CedarGroveStudios/Musique_Concrete_Clock/PCB/Musique_Concrete_Clock.png

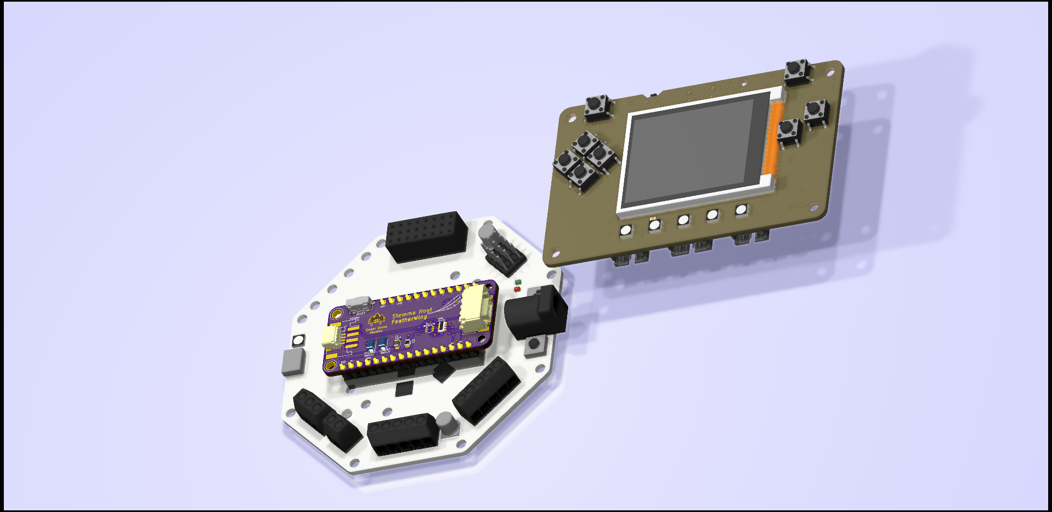
PCB/Musique_Concrete_Clock.png
