CedarGroveStudios/Musique_Concrete_Clock/photos and graphics/DSC06083 2.jpeg

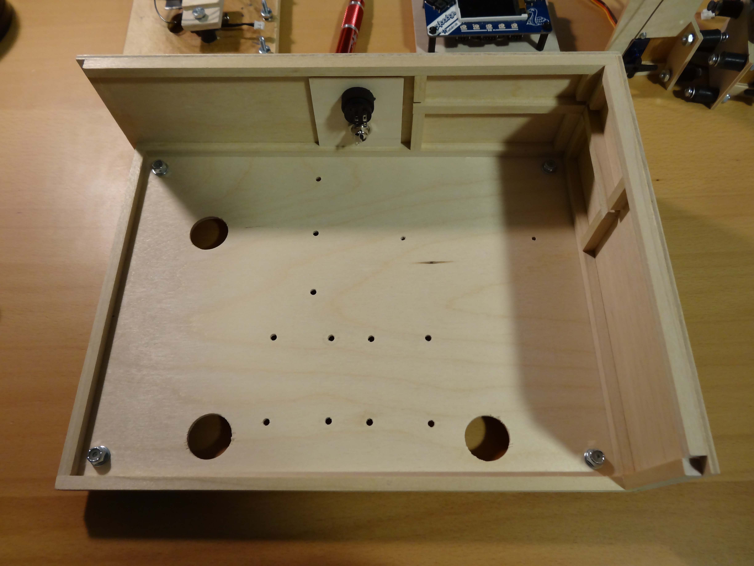
photos and graphics/DSC06083 2.jpeg
