CedarGroveStudios/Musique_Concrete_Clock/photos and graphics/DSC06085 2.jpeg

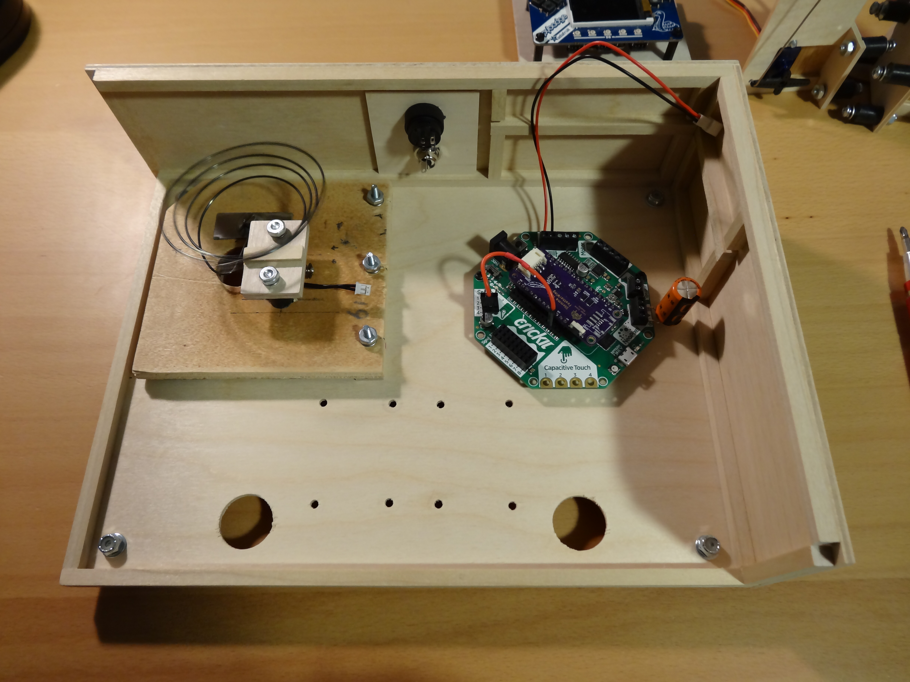
photos and graphics/DSC06085 2.jpeg
