CedarGroveStudios/Musique_Concrete_Clock/photos and graphics/DSC06090 2.jpeg

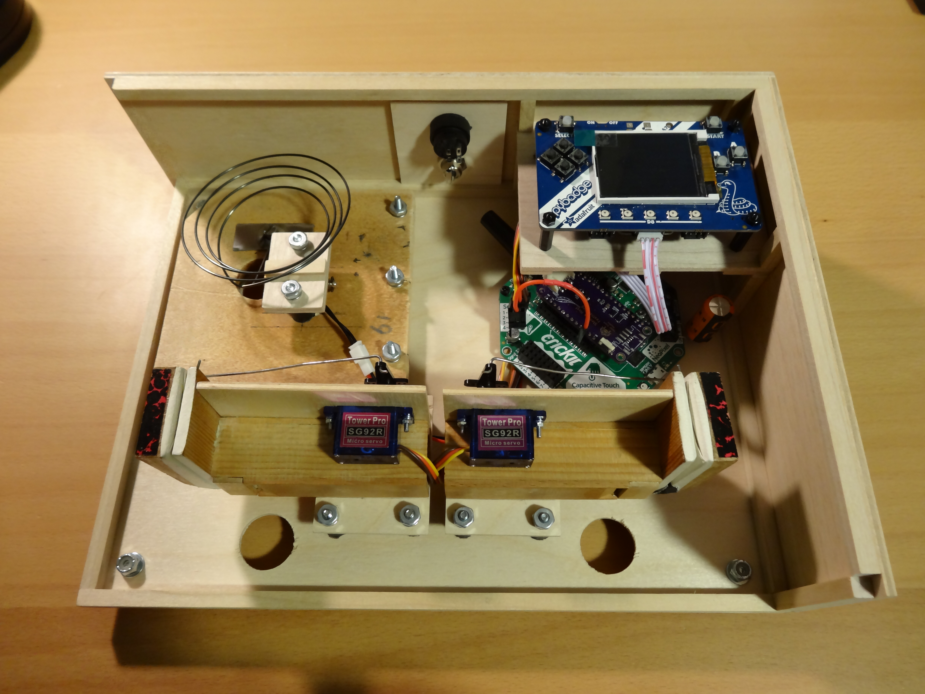
photos and graphics/DSC06090 2.jpeg
