CedarGroveStudios/Musique_Concrete_Clock/photos and graphics/DSC06091 2.jpeg

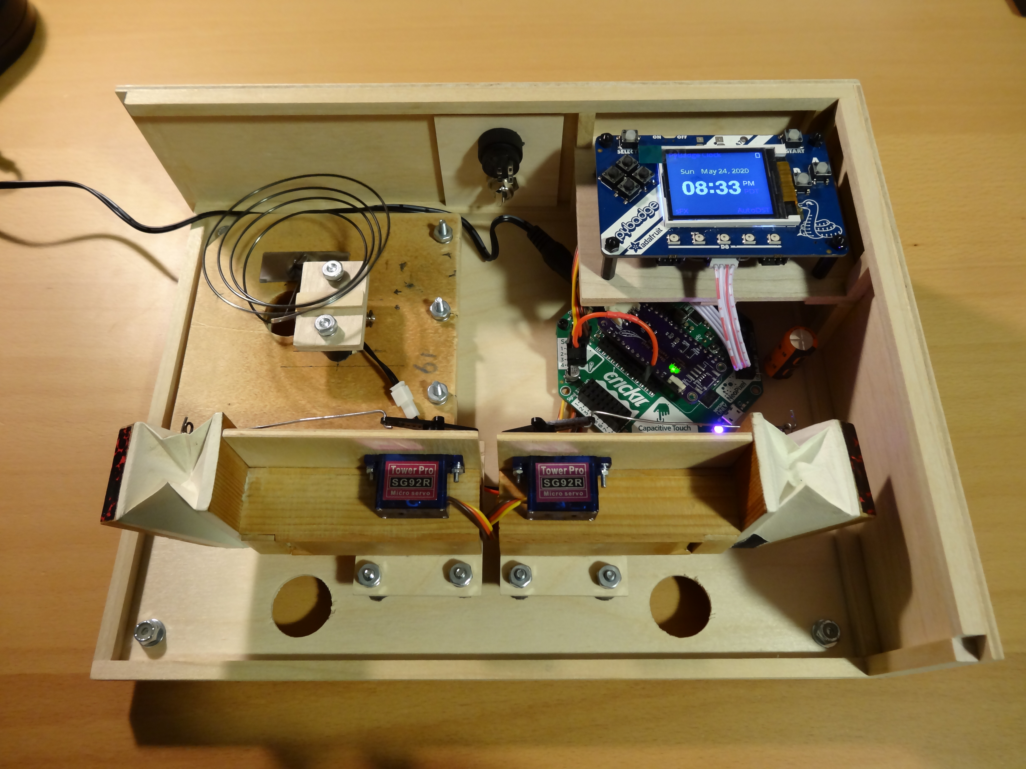
photos and graphics/DSC06091 2.jpeg
