CedarGroveStudios/Musique_Concrete_Clock/photos and graphics/DSC06096.jpeg

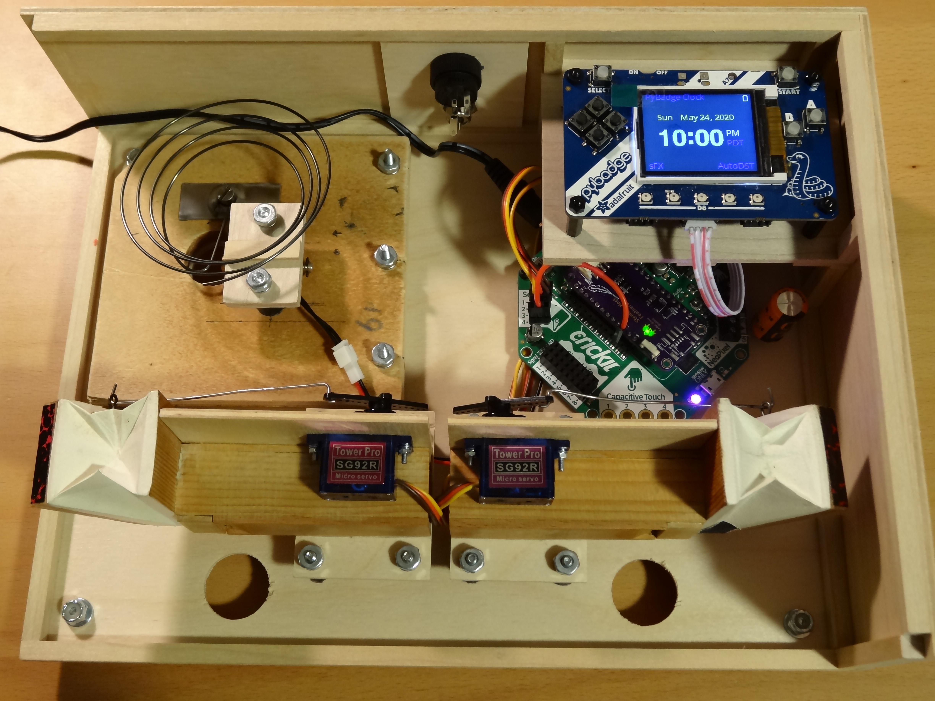
photos and graphics/DSC06096.jpeg
