CedarGroveStudios/Musique_Concrete_Clock/photos and graphics/IMG_0173.jpeg

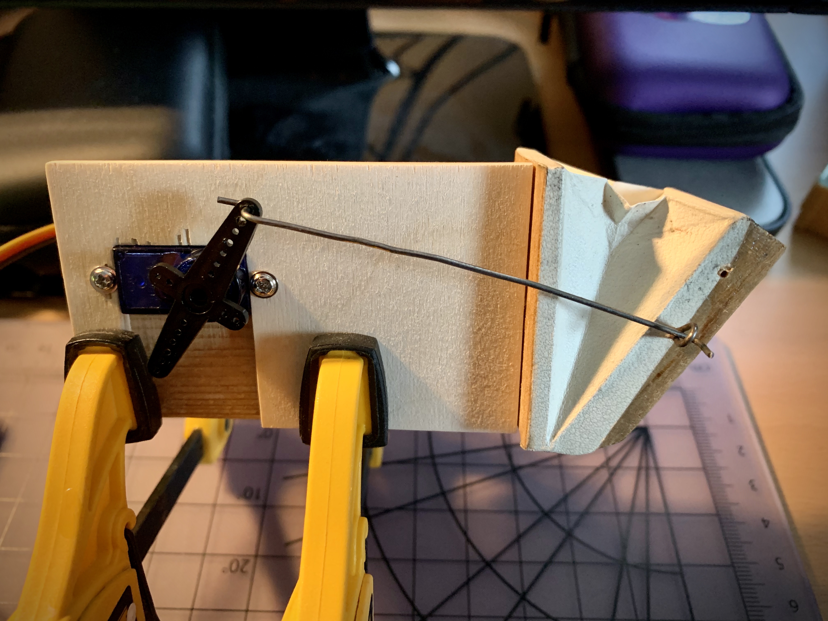
photos and graphics/IMG_0173.jpeg
