CedarGroveStudios/Musique_Concrete_Clock/photos and graphics/IMG_0174.jpeg

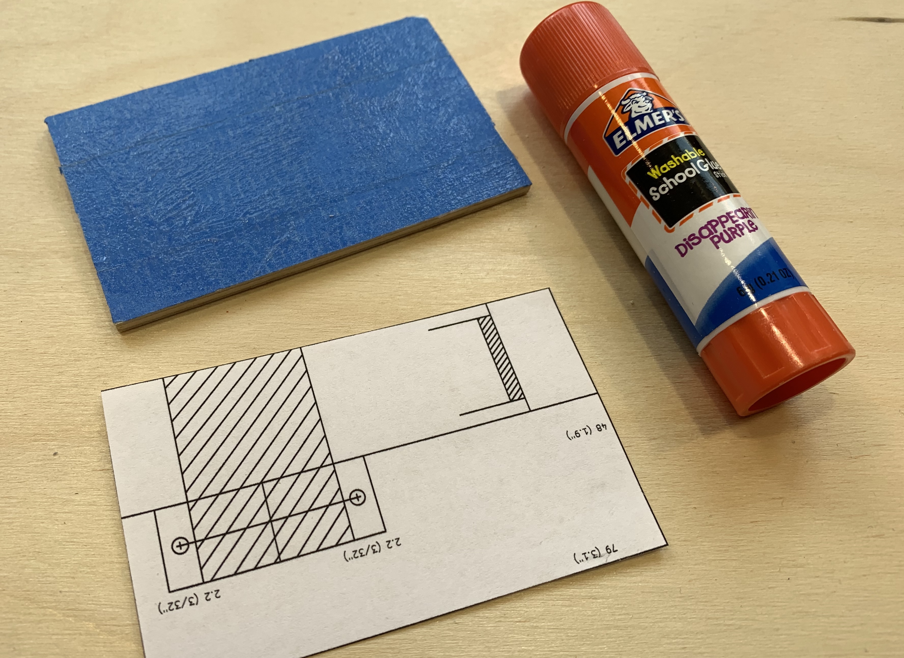
photos and graphics/IMG_0174.jpeg
