CedarGroveStudios/Musique_Concrete_Clock/photos and graphics/IMG_0175.jpeg

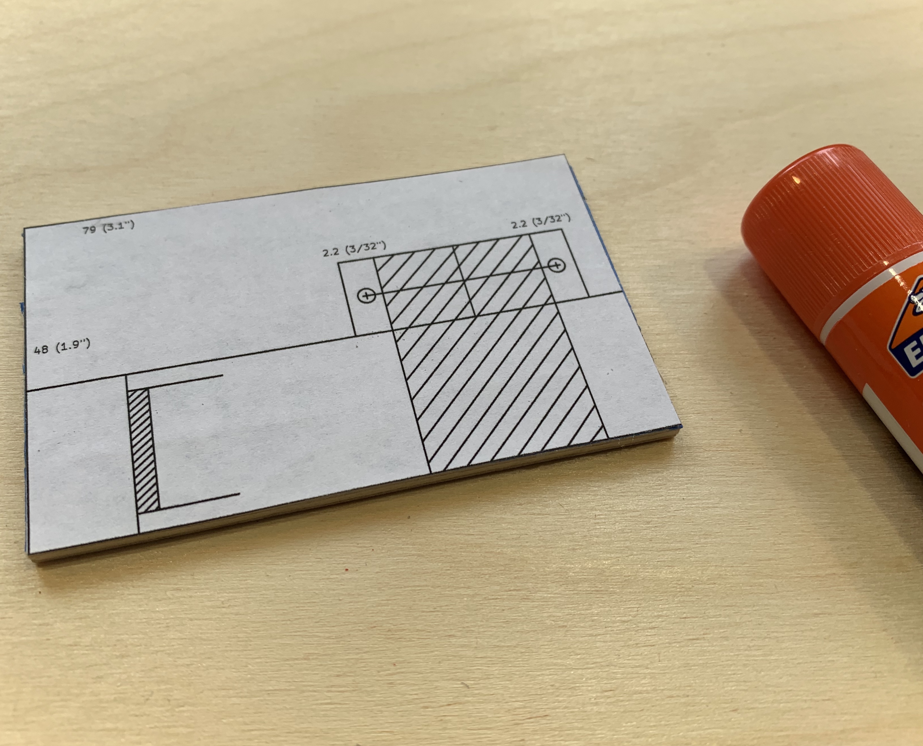
photos and graphics/IMG_0175.jpeg
