CedarGroveStudios/Musique_Concrete_Clock/photos and graphics/IMG_0176.jpeg

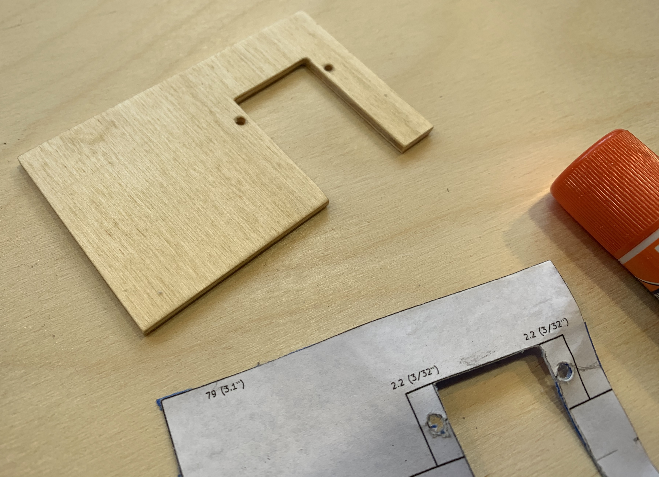
photos and graphics/IMG_0176.jpeg
