CedarGroveStudios/Musique_Concrete_Clock/photos and graphics/IMG_0180.jpg

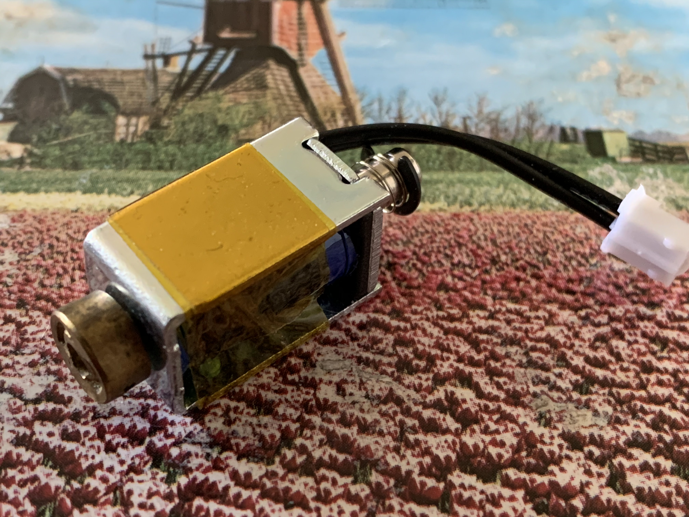
photos and graphics/IMG_0180.jpg
