CedarGroveStudios/Musique_Concrete_Clock/photos and graphics/IMG_0204.jpeg

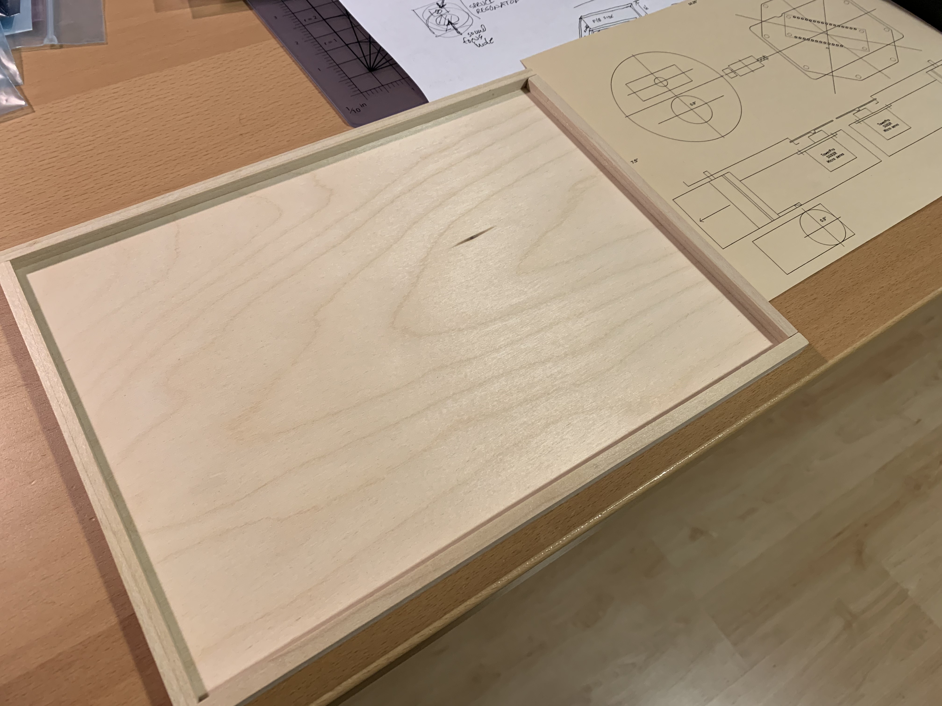
photos and graphics/IMG_0204.jpeg
