CedarGroveStudios/Musique_Concrete_Clock/photos and graphics/IMG_0205.jpeg

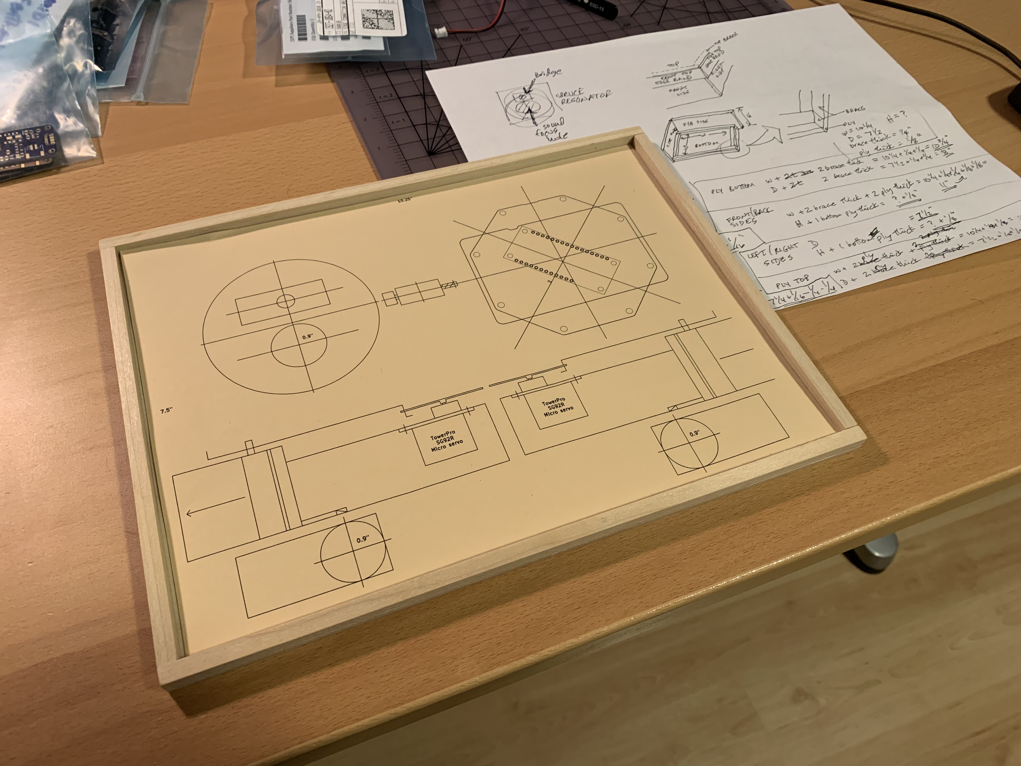
photos and graphics/IMG_0205.jpeg
