CedarGroveStudios/Musique_Concrete_Clock/photos and graphics/IMG_0206.jpeg

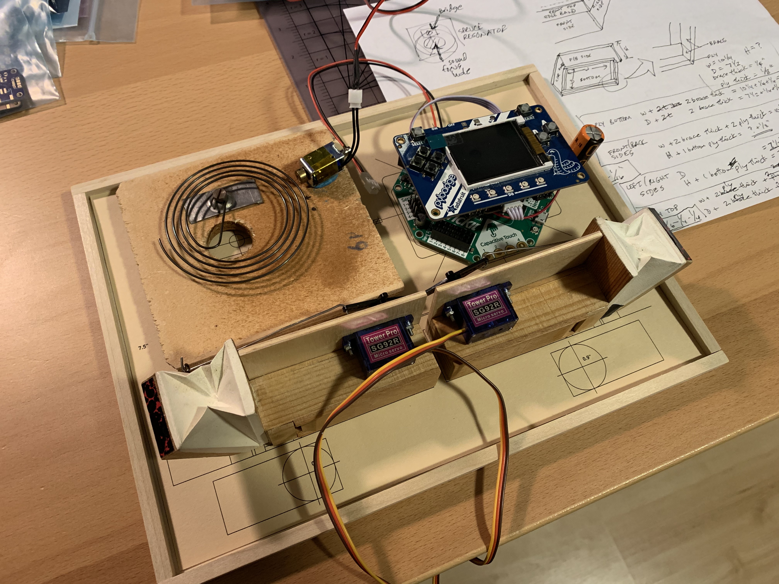
photos and graphics/IMG_0206.jpeg
