CedarGroveStudios/Musique_Concrete_Clock/photos and graphics/IMG_0208.jpeg

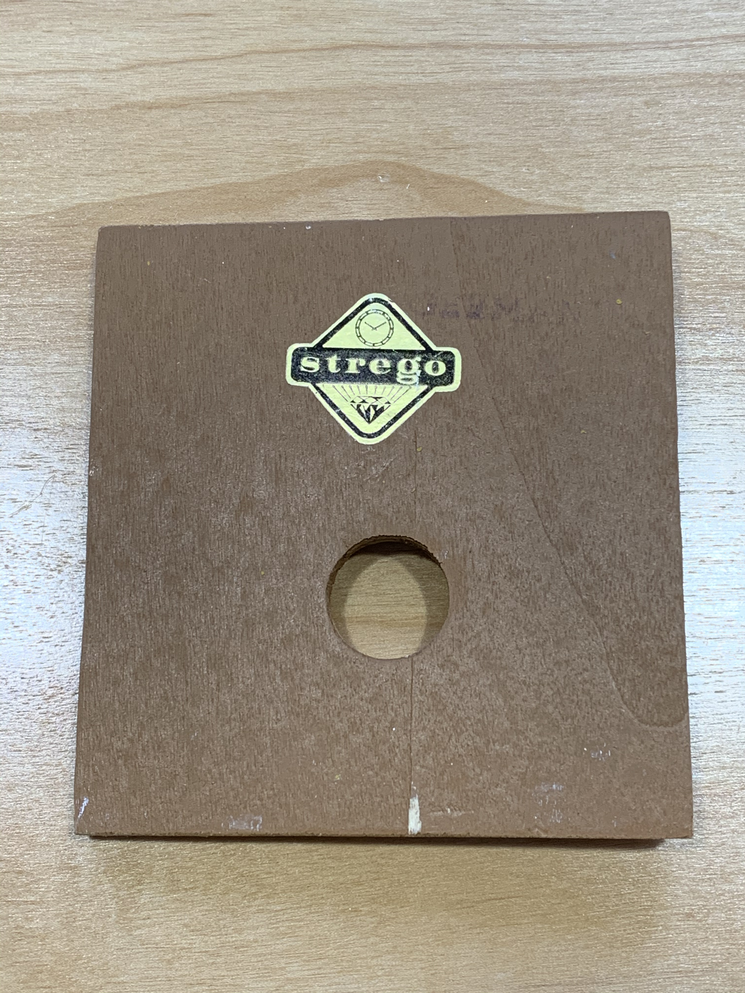
photos and graphics/IMG_0208.jpeg
