CedarGroveStudios/Musique_Concrete_Clock/photos and graphics/IMG_0209.jpeg

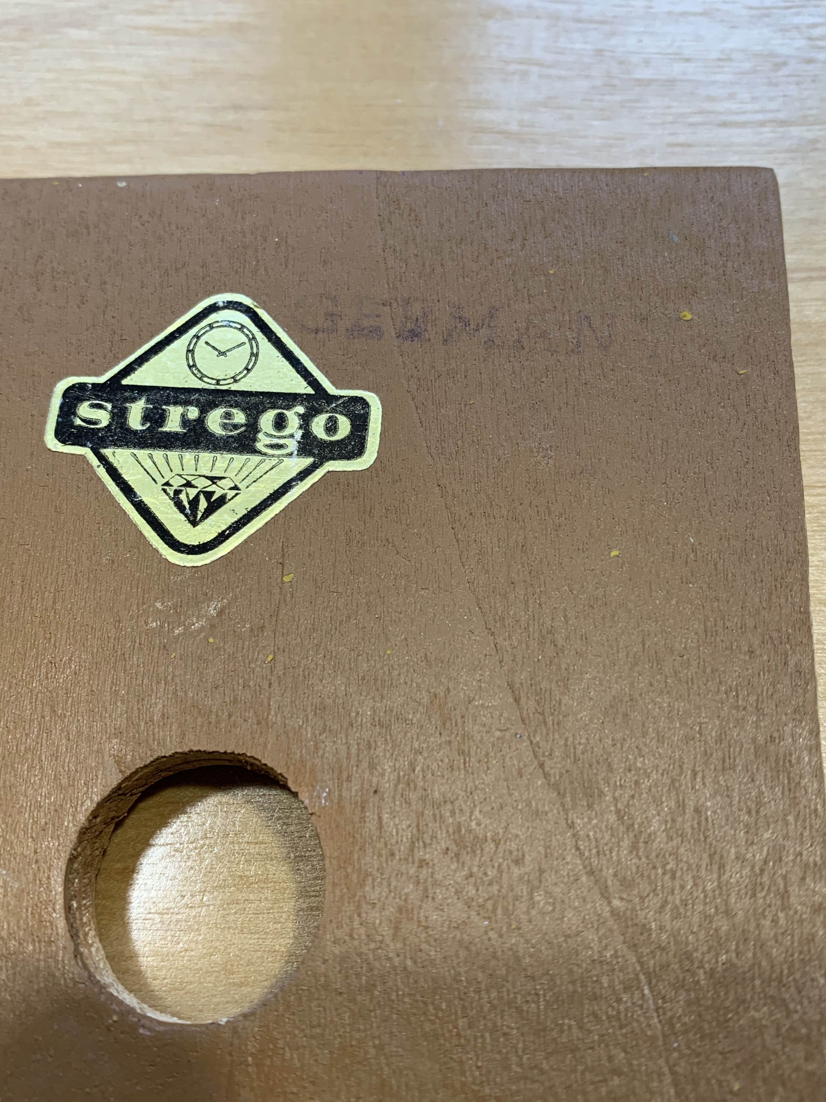
photos and graphics/IMG_0209.jpeg
