CedarGroveStudios/Musique_Concrete_Clock/photos and graphics/IMG_0211.jpeg

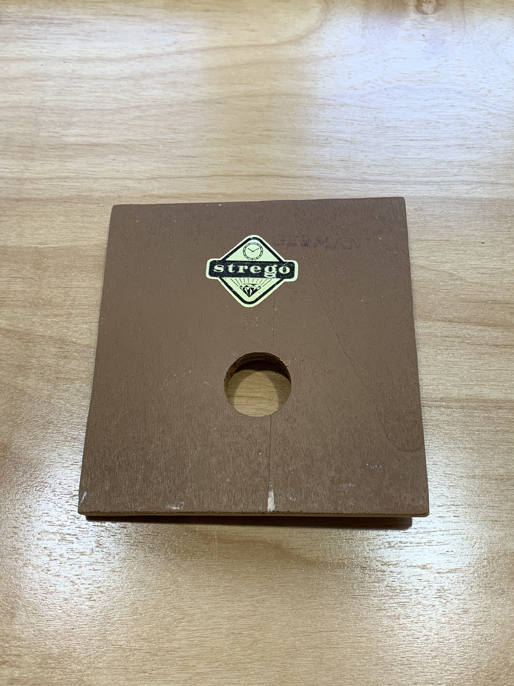
photos and graphics/IMG_0211.jpeg
