CedarGroveStudios/Musique_Concrete_Clock/photos and graphics/IMG_0227.jpeg

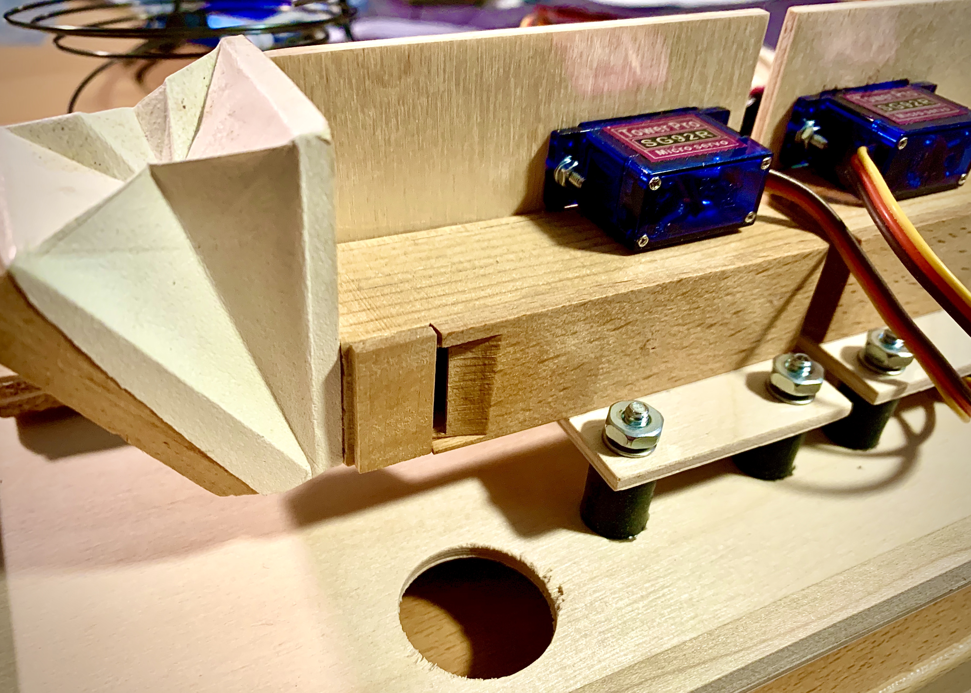
photos and graphics/IMG_0227.jpeg
