CedarGroveStudios/Musique_Concrete_Clock/photos and graphics/IMG_0228.jpeg

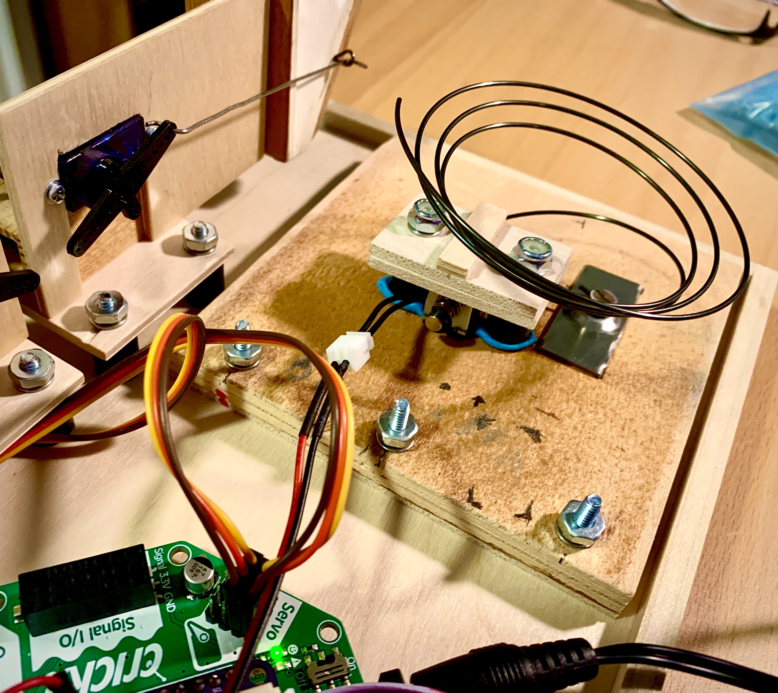
photos and graphics/IMG_0228.jpeg
