CedarGroveStudios/Musique_Concrete_Clock/photos and graphics/IMG_0229.jpeg

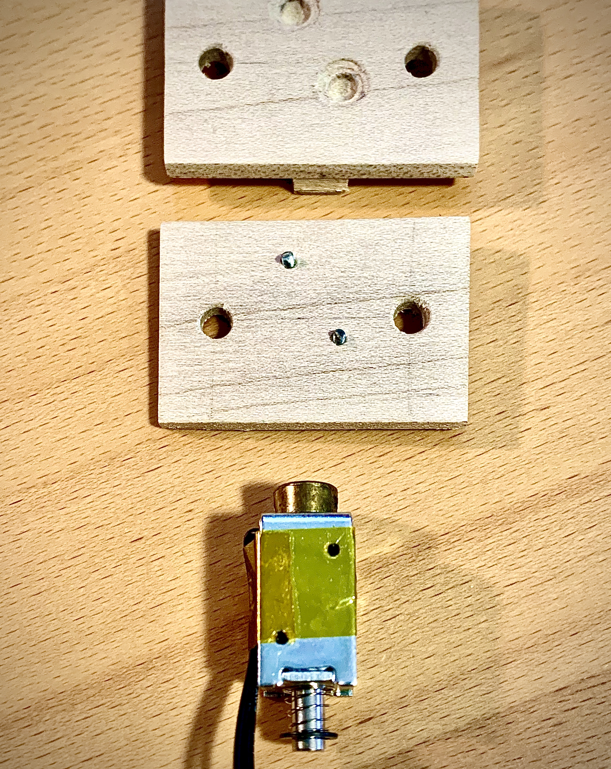
photos and graphics/IMG_0229.jpeg
