CedarGroveStudios/Musique_Concrete_Clock/photos and graphics/IMG_0232.jpeg

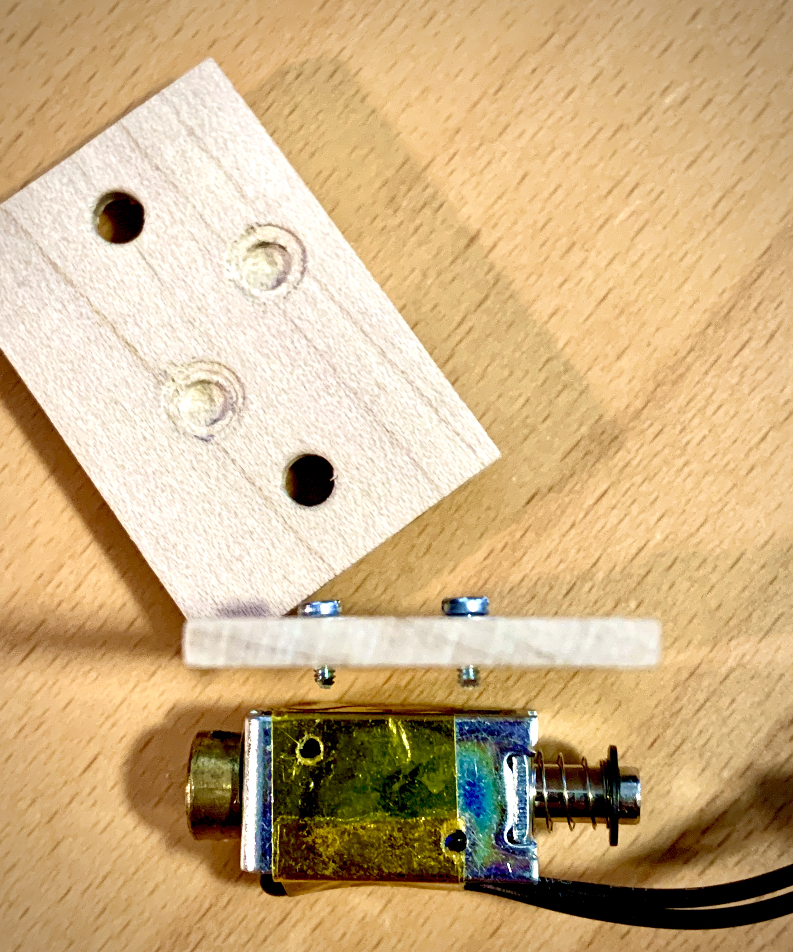
photos and graphics/IMG_0232.jpeg
