CedarGroveStudios/Musique_Concrete_Clock/photos and graphics/IMG_0235 2.jpeg

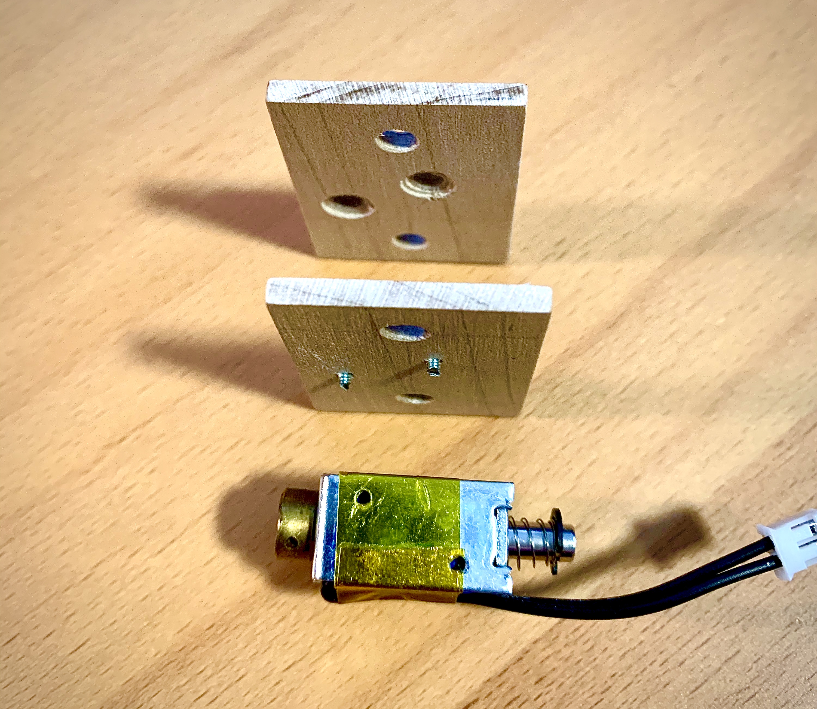
photos and graphics/IMG_0235 2.jpeg
