CedarGroveStudios/Musique_Concrete_Clock/photos and graphics/IMG_0237.jpeg

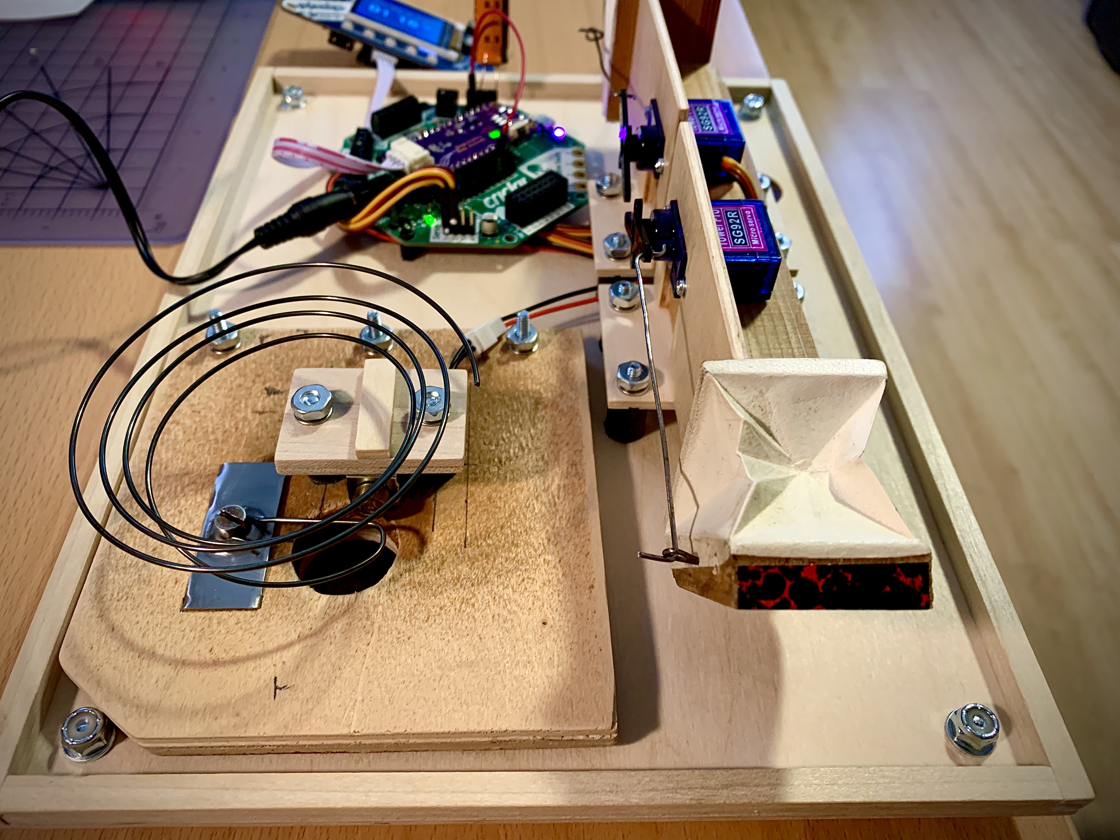
photos and graphics/IMG_0237.jpeg
