CedarGroveStudios/Musique_Concrete_Clock/photos and graphics/IMG_0238.jpeg

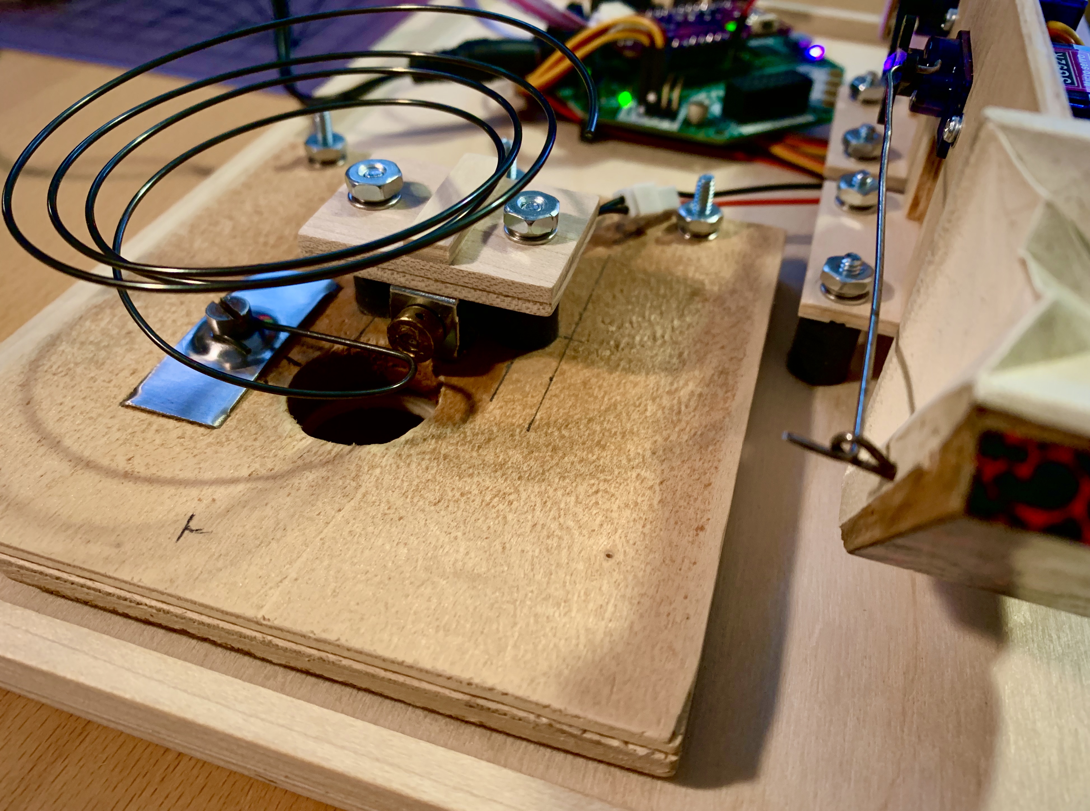
photos and graphics/IMG_0238.jpeg
