CedarGroveStudios/Musique_Concrete_Clock/photos and graphics/IMG_0239.jpeg

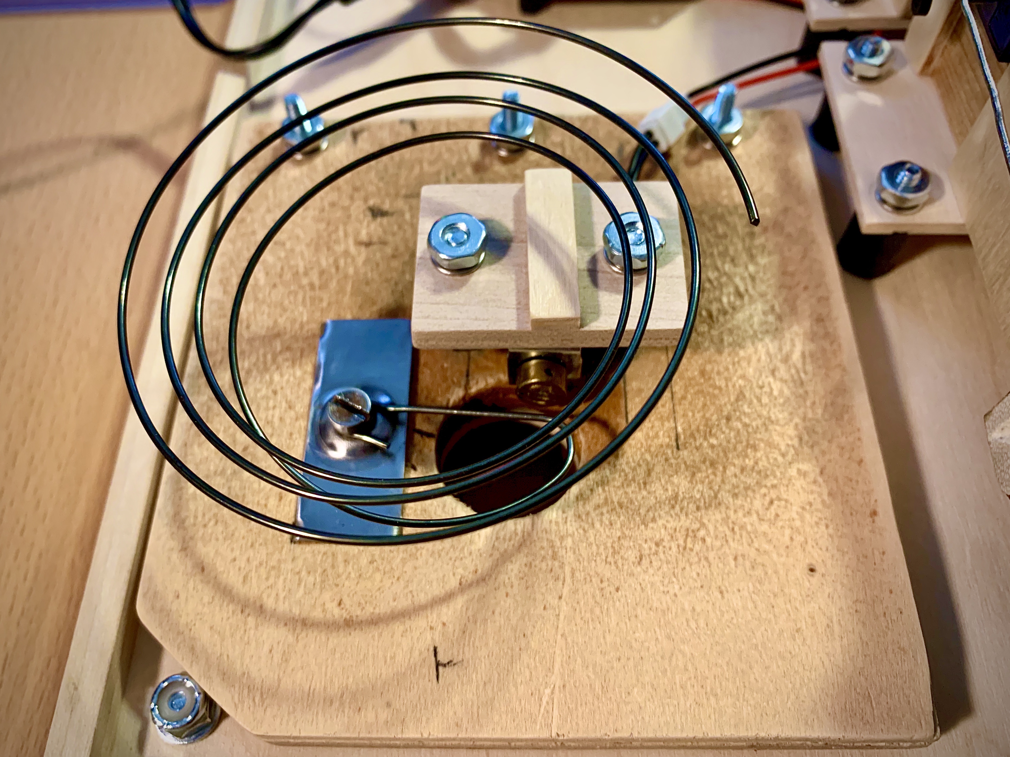
photos and graphics/IMG_0239.jpeg
