CedarGroveStudios/Musique_Concrete_Clock/photos and graphics/IMG_0248.jpeg

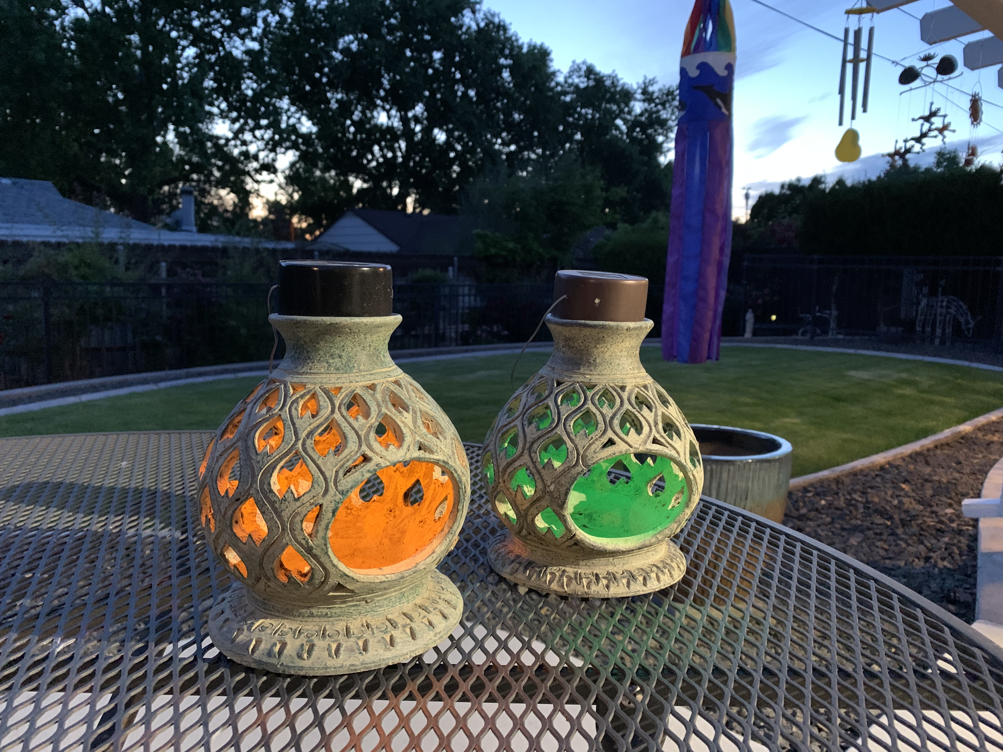
photos and graphics/IMG_0248.jpeg
