CedarGroveStudios/Musique_Concrete_Clock/photos and graphics/IMG_0261.jpeg

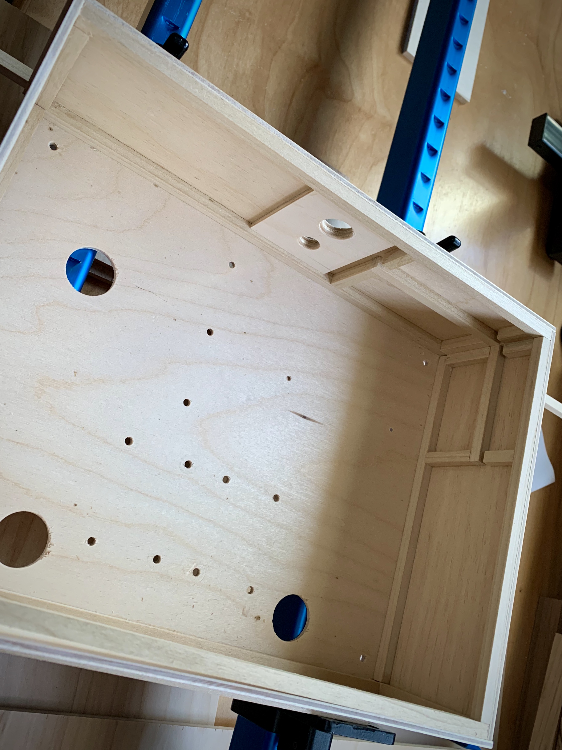
photos and graphics/IMG_0261.jpeg
