CedarGroveStudios/Musique_Concrete_Clock/photos and graphics/IMG_0262.jpeg

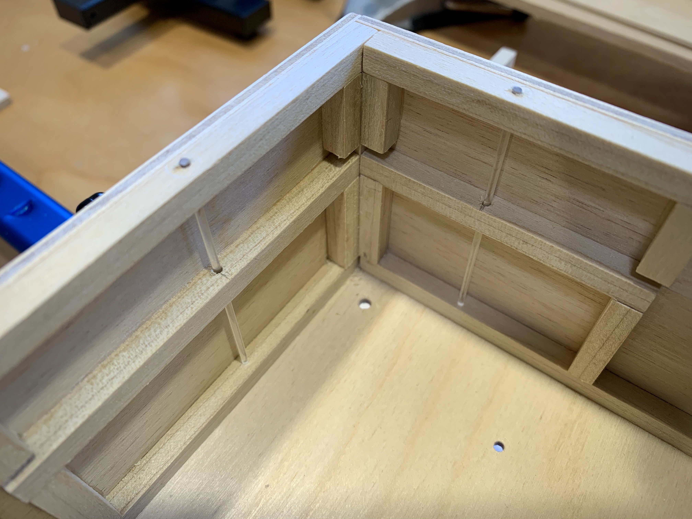
photos and graphics/IMG_0262.jpeg
