CedarGroveStudios/Musique_Concrete_Clock/photos and graphics/IMG_0263.jpeg

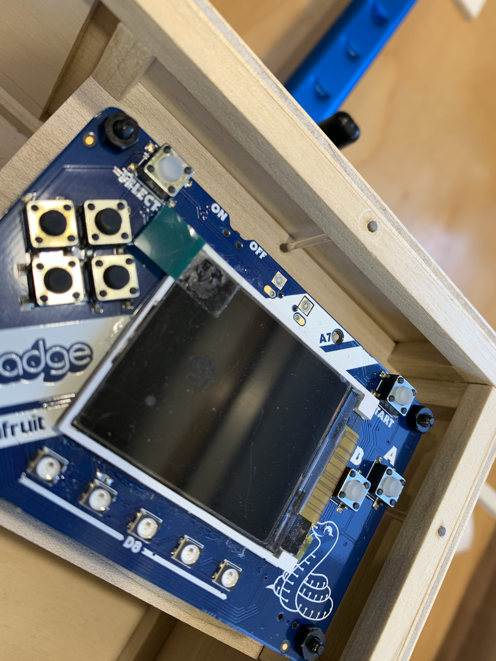
photos and graphics/IMG_0263.jpeg
