CedarGroveStudios/Musique_Concrete_Clock/photos and graphics/IMG_0264.jpeg

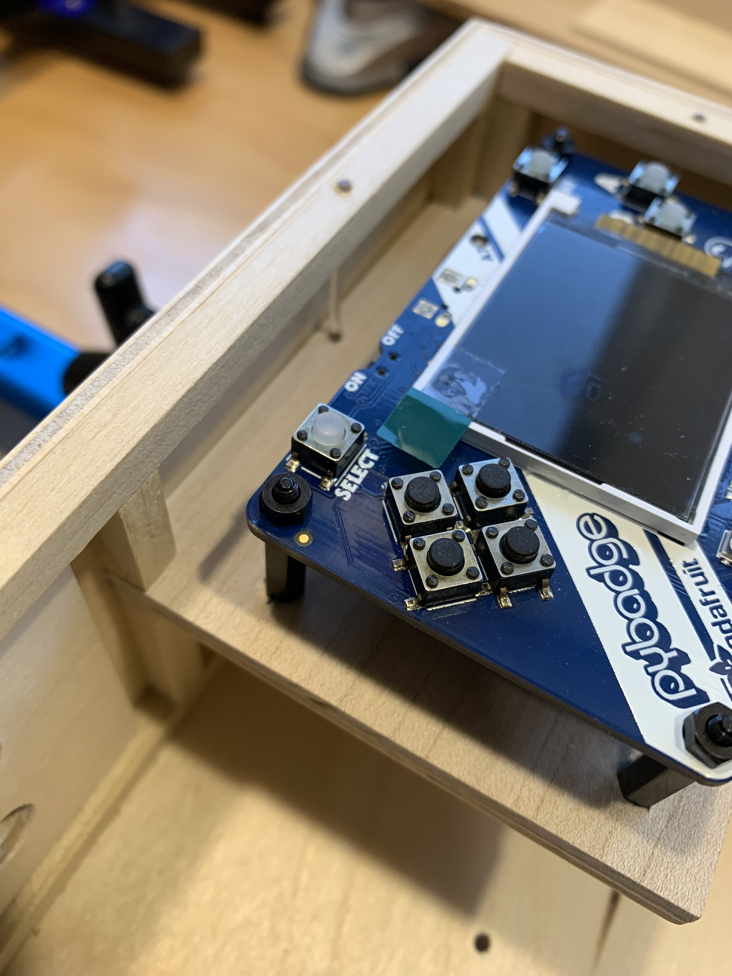
photos and graphics/IMG_0264.jpeg
