CedarGroveStudios/Musique_Concrete_Clock/photos and graphics/IMG_0269.jpeg

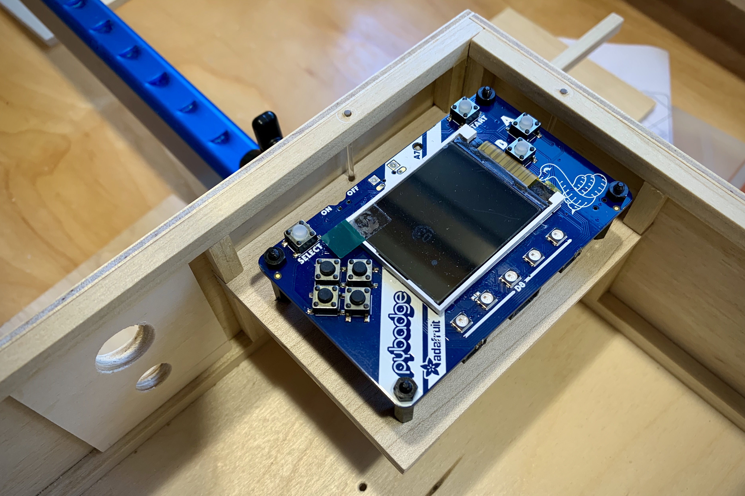
photos and graphics/IMG_0269.jpeg
