CedarGroveStudios/Musique_Concrete_Clock/photos and graphics/IMG_0273.jpeg

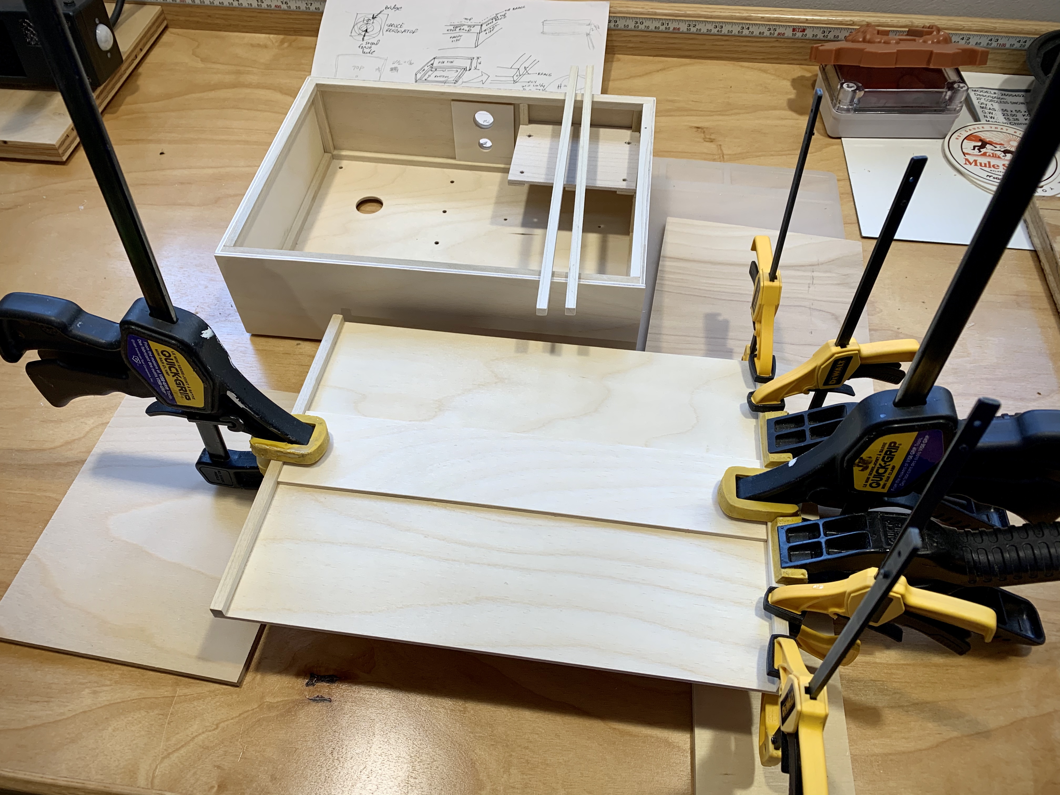
photos and graphics/IMG_0273.jpeg
