CedarGroveStudios/Musique_Concrete_Clock/photos and graphics/MCC_box_1.jpg

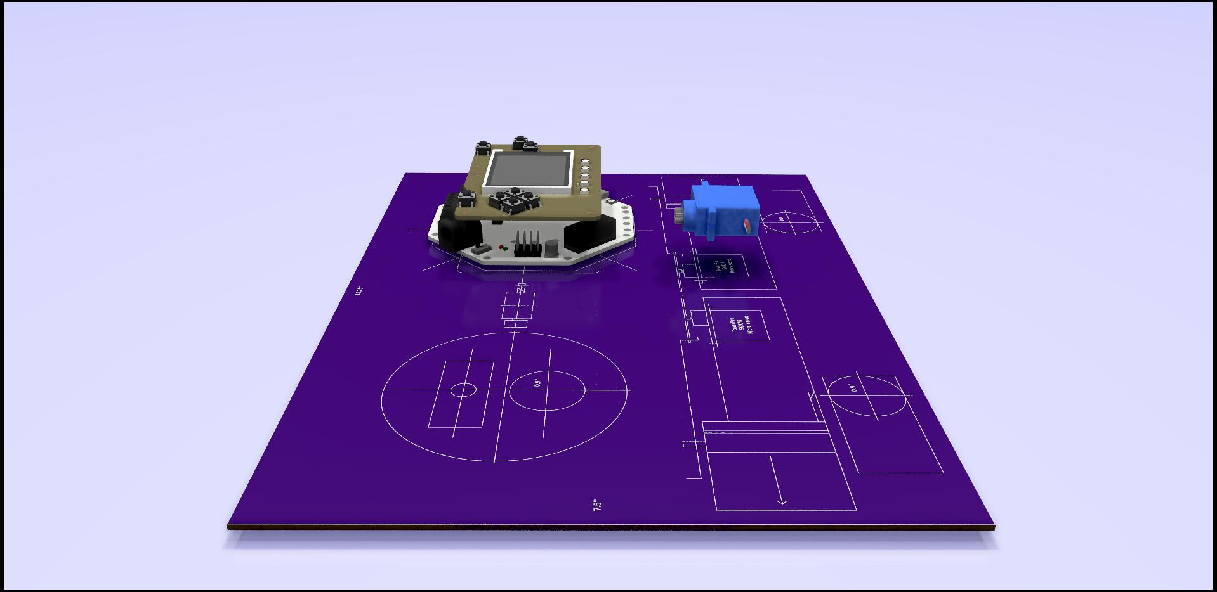
photos and graphics/MCC_box_1.jpg
