CedarGroveStudios/Musique_Concrete_Clock/photos and graphics/MCC_box_2.jpg

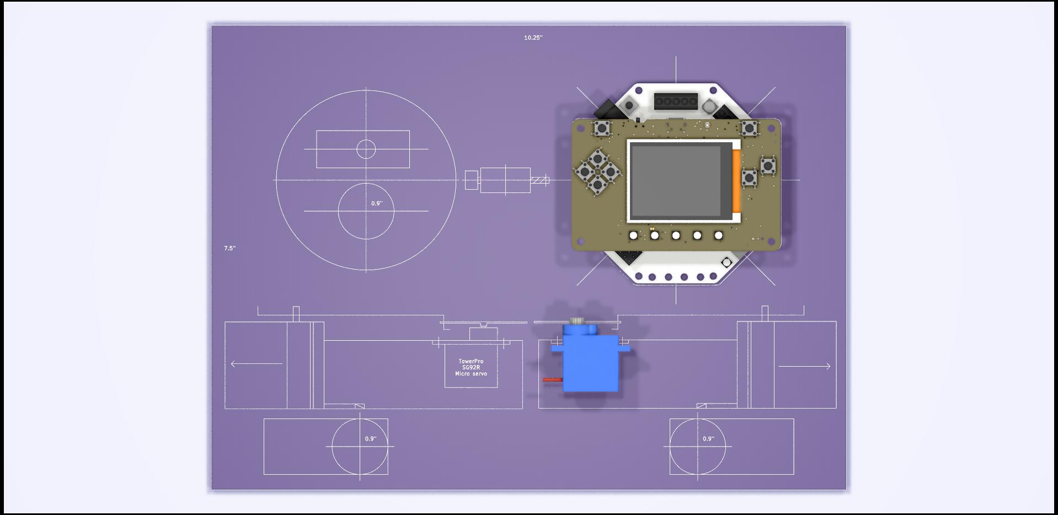
photos and graphics/MCC_box_2.jpg
