CedarGroveStudios/Musique_Concrete_Clock/photos and graphics/IMG_0210.jpeg

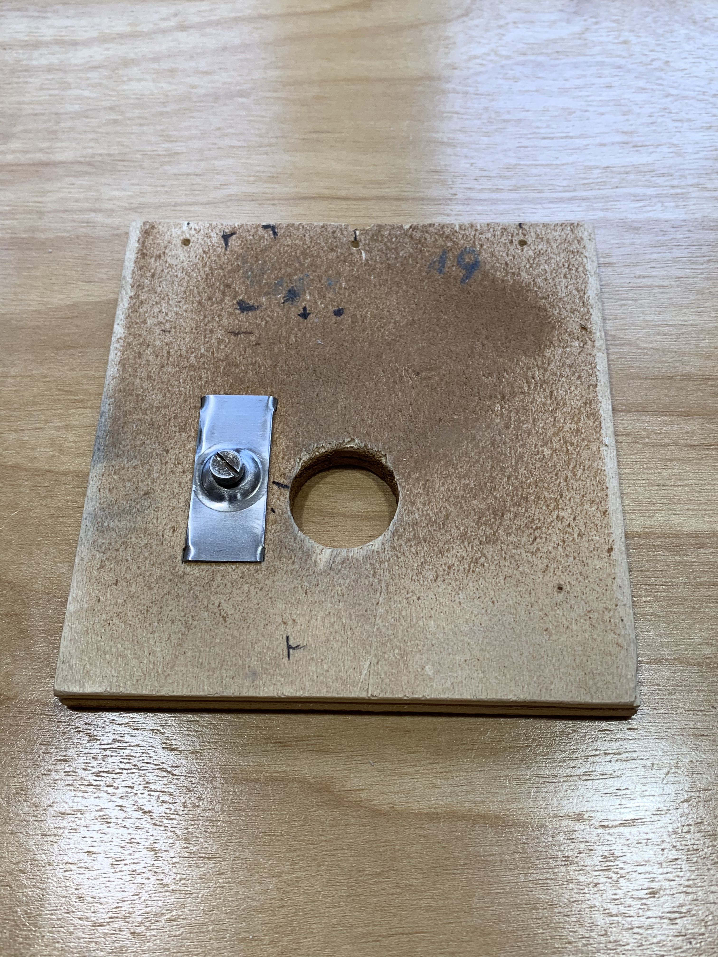
photos and graphics/IMG_0210.jpeg
